impatrq/insonora/Estructura/corte circular de la caja de insonora para que el publico pueda interactuar/Imagen de WhatsApp 2023-11-22 a las 09.19.30_ffd868a9.jpg

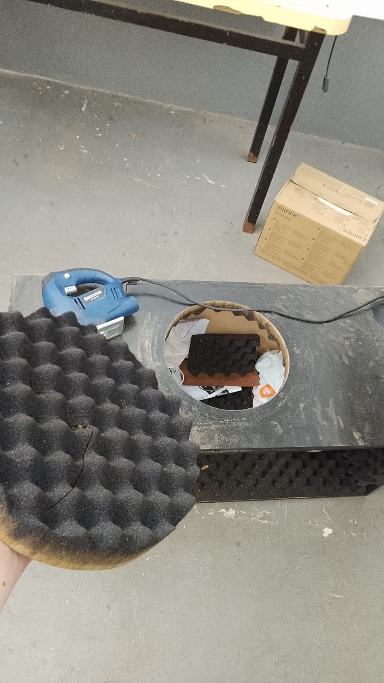
Estructura/corte circular de la caja de insonora para que el publico pueda interactuar/Imagen de WhatsApp 2023-11-22 a las 09.19.30_ffd868a9.jpg
