impatrq/insonora/Estructura/cortes de la madera para hacer la caja de insonora/Imagen de WhatsApp 2023-11-22 a las 09.21.23_7561fe22.jpg

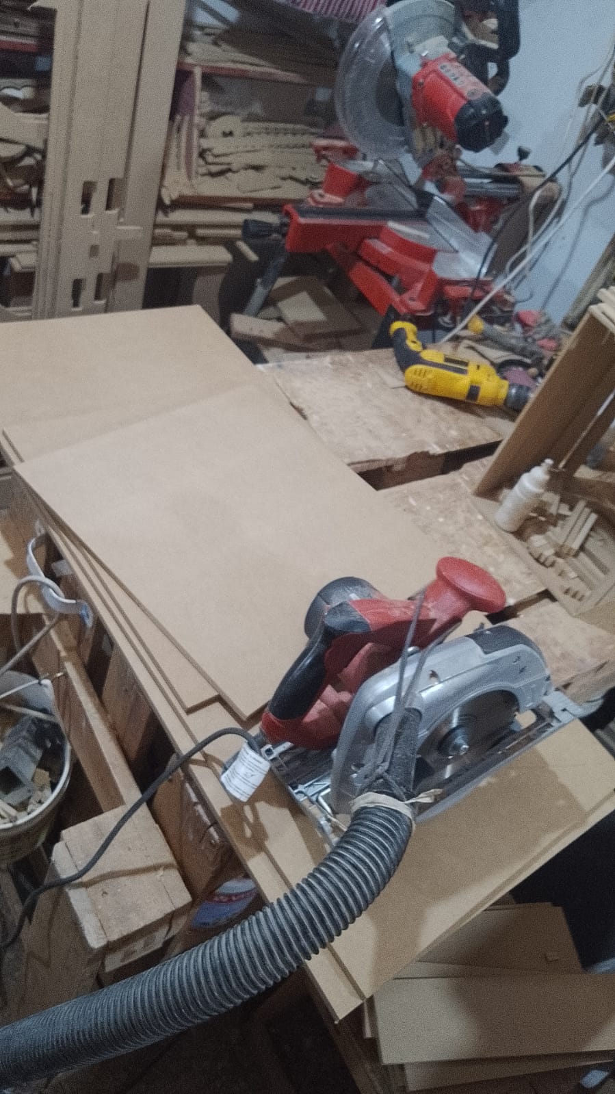
Estructura/cortes de la madera para hacer la caja de insonora/Imagen de WhatsApp 2023-11-22 a las 09.21.23_7561fe22.jpg
