impatrq/insonora/Estructura/disposicion de parlantes/Imagen de WhatsApp 2023-11-22 a las 09.26.25_6fa25fe4.jpg

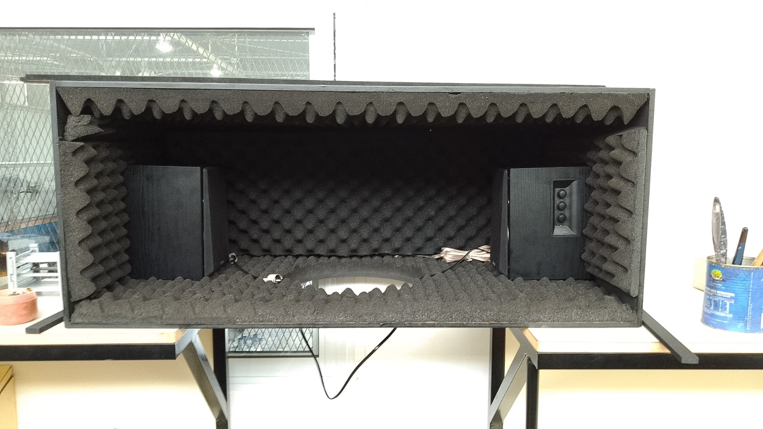
Estructura/disposicion de parlantes/Imagen de WhatsApp 2023-11-22 a las 09.26.25_6fa25fe4.jpg
