impatrq/insonora/Estructura/Imagen de WhatsApp 2023-11-22 a las 09.16.47_289416f6.jpg

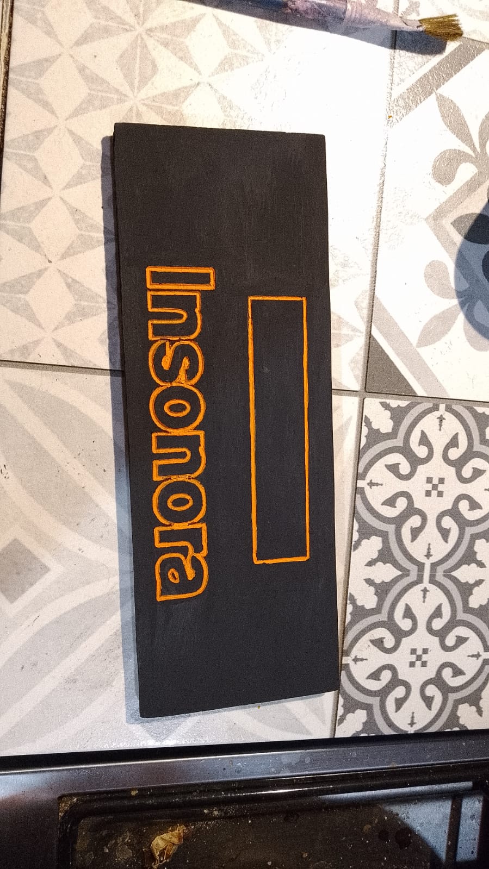
Estructura/Imagen de WhatsApp 2023-11-22 a las 09.16.47_289416f6.jpg
