impatrq/insonora/Estructura/plano a escala de la caja de insonora/Imagen de WhatsApp 2023-11-22 a las 09.17.45_47281ffb.jpg

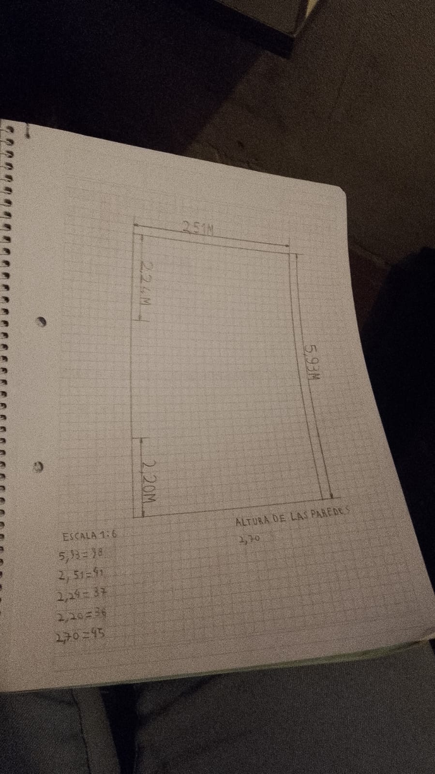
Estructura/plano a escala de la caja de insonora/Imagen de WhatsApp 2023-11-22 a las 09.17.45_47281ffb.jpg
