impatrq/insonora/fotos/pcb-pwm-audio-terminado.jpeg

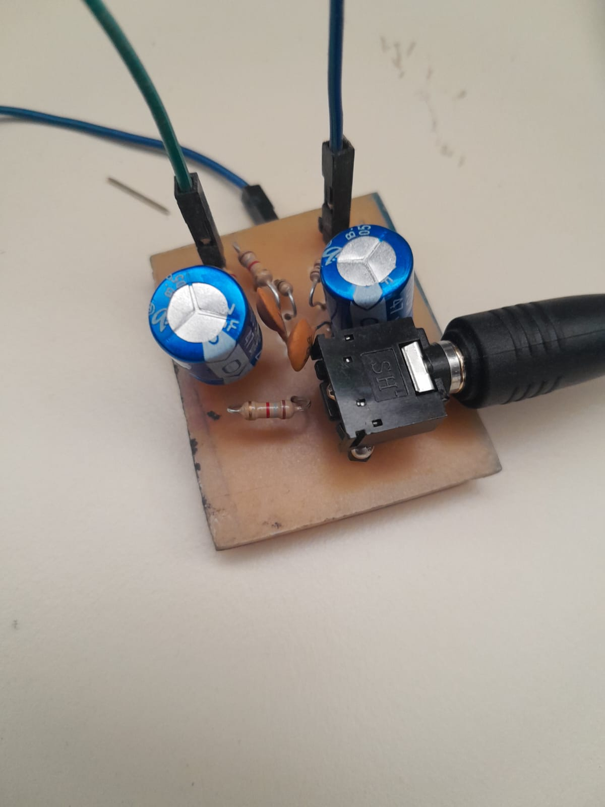
fotos/pcb-pwm-audio-terminado.jpeg
