impatrq/insonora/PCBS/cortes plaquetas de cobre/Imagen de WhatsApp 2023-11-22 a las 09.17.11_49b71000.jpg

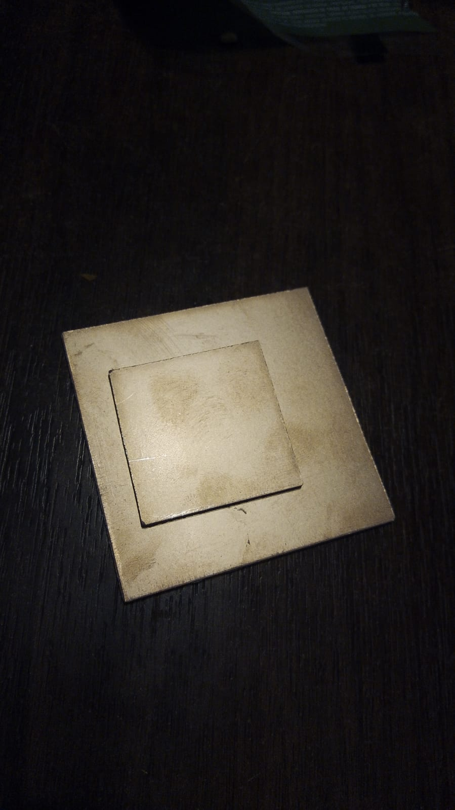
PCBS/cortes plaquetas de cobre/Imagen de WhatsApp 2023-11-22 a las 09.17.11_49b71000.jpg
