impatrq/insonora/Post-no-subidos/Ambientes laborales (1).png

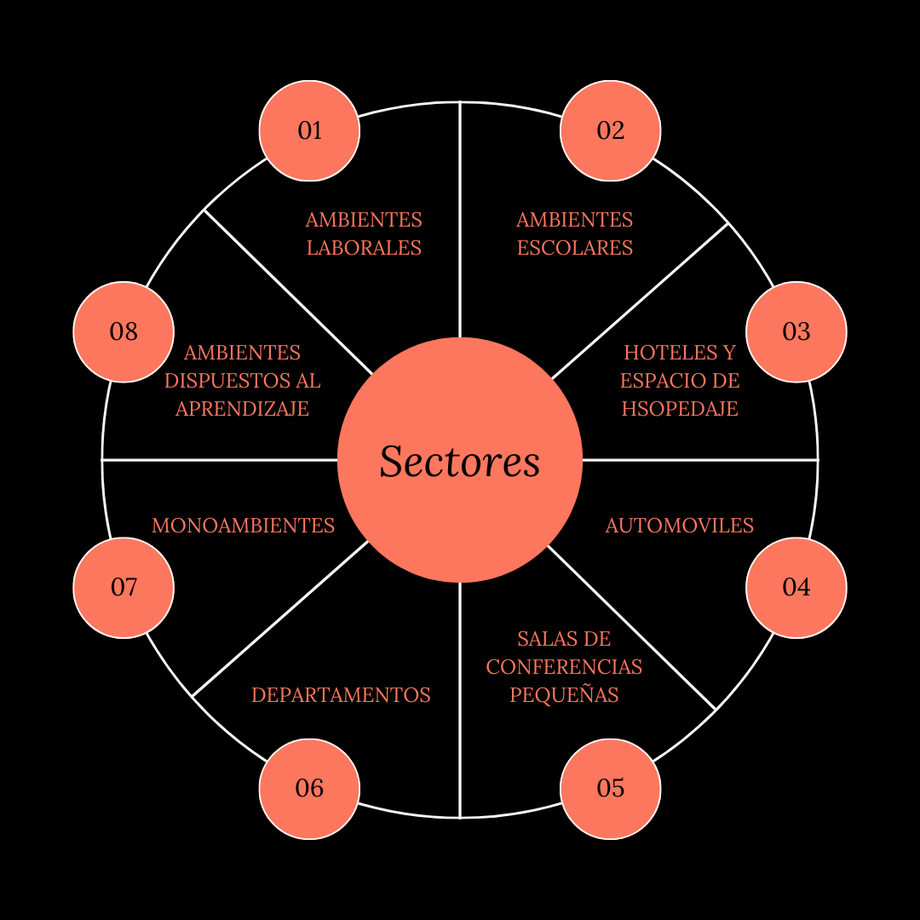
Post-no-subidos/Ambientes laborales (1).png
