impatrq/insonora/Post-no-subidos/beneficios de la descontaminacion sonora (1).png

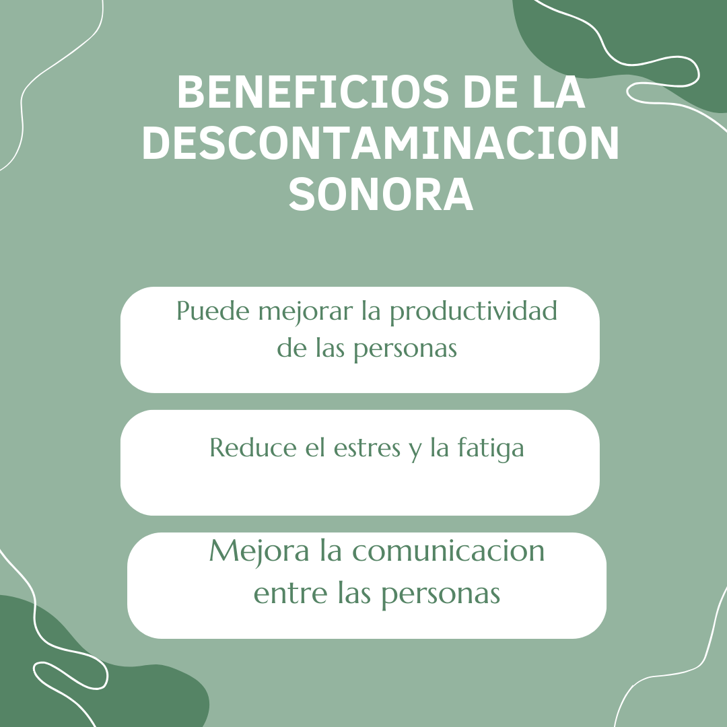
Post-no-subidos/beneficios de la descontaminacion sonora (1).png
