impatrq/insonora/Post-no-subidos/Captura de pantalla 2023-11-24 145829.png

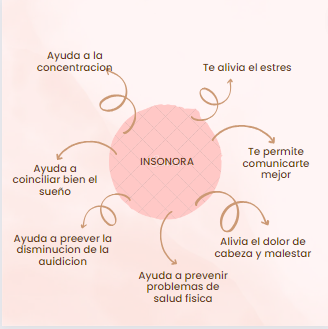
Post-no-subidos/Captura de pantalla 2023-11-24 145829.png
