impatrq/insonora/Post-no-subidos/Desventajas de la contaminacion sonora.png

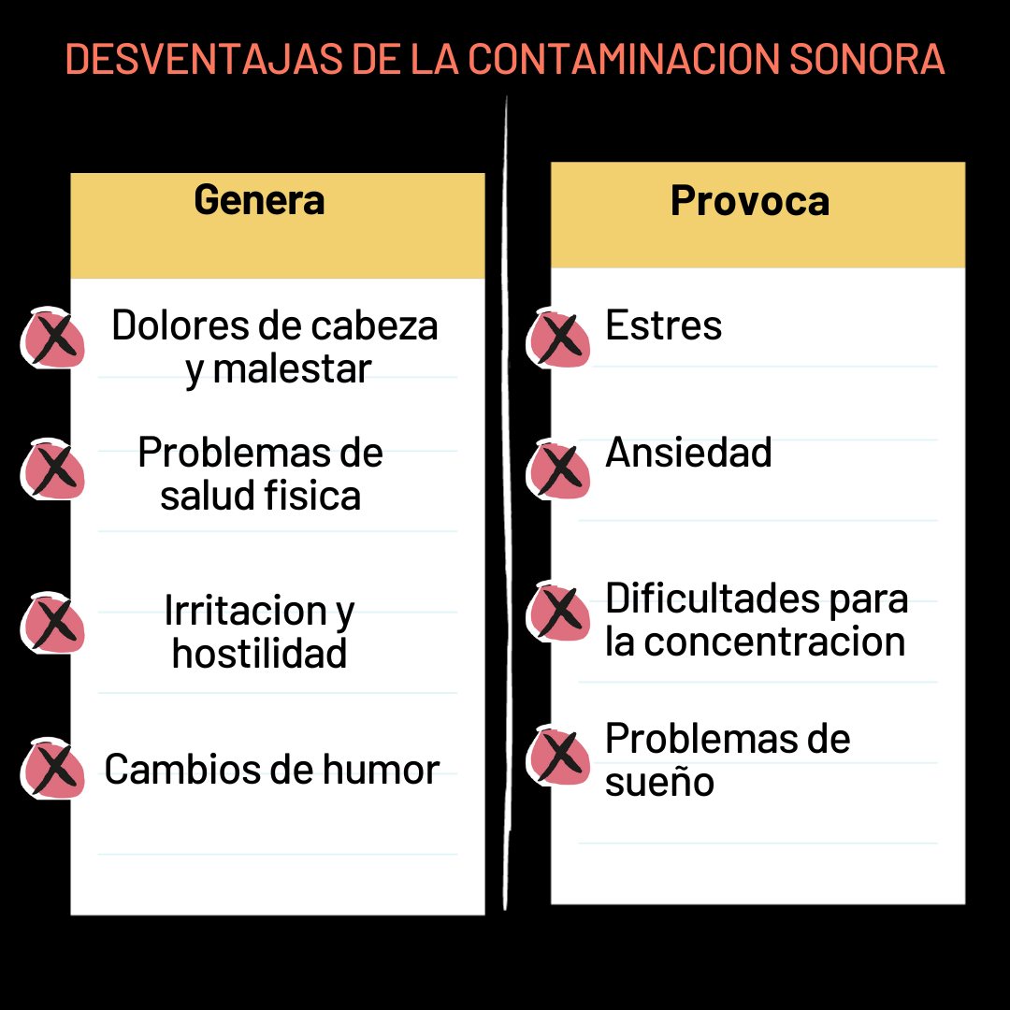
Post-no-subidos/Desventajas de la contaminacion sonora.png
