impatrq/insonora/Post-no-subidos/Dia nacional de la audicion.png

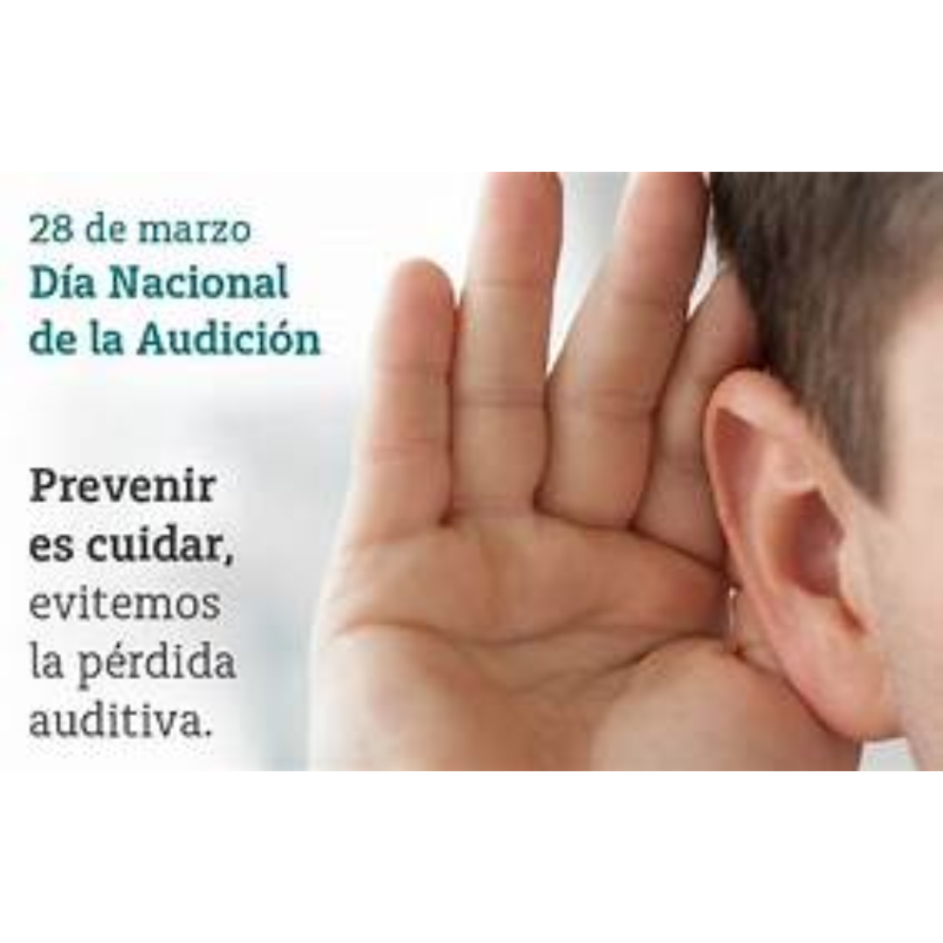
Post-no-subidos/Dia nacional de la audicion.png
