impatrq/insonora/Post-no-subidos/Efectos del ruido.png

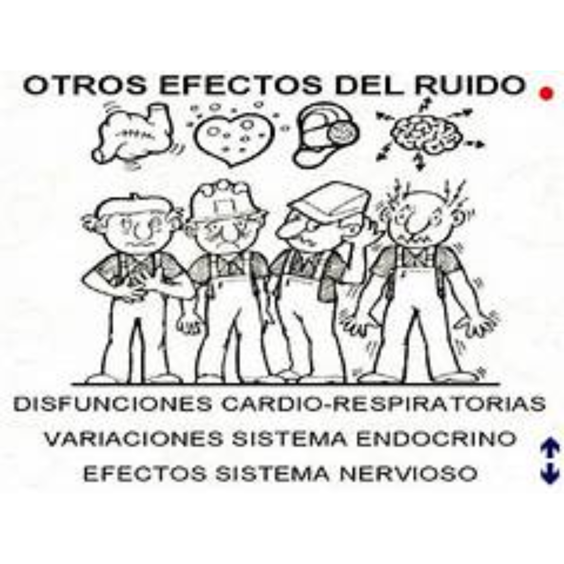
Post-no-subidos/Efectos del ruido.png
