impatrq/insonora/Post-no-subidos/El ruido es un sonido no deseado que puede generar molestias en la sociedad (2).png

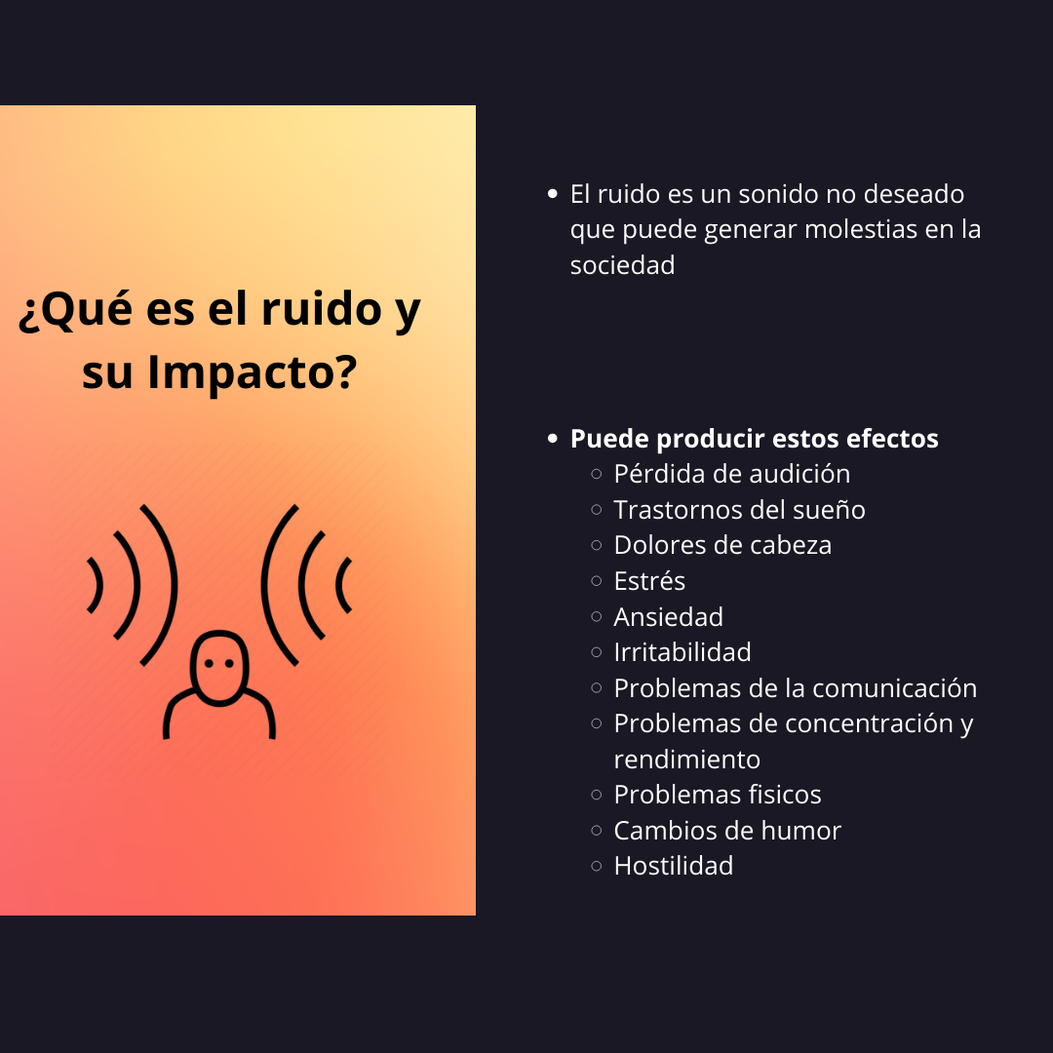
Post-no-subidos/El ruido es un sonido no deseado que puede generar molestias en la sociedad (2).png
