impatrq/insonora/Post-no-subidos/Sabias que.png

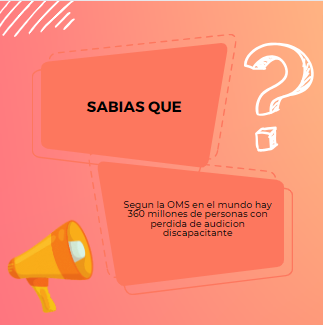
Post-no-subidos/Sabias que.png
