impatrq/insonora/Post-no-subidos/Vengan a vernos el dia viernes 1011 y el dia sabado 1111 a la exposicion anual que se realiza en la escuela tecnica n°7 (1).png

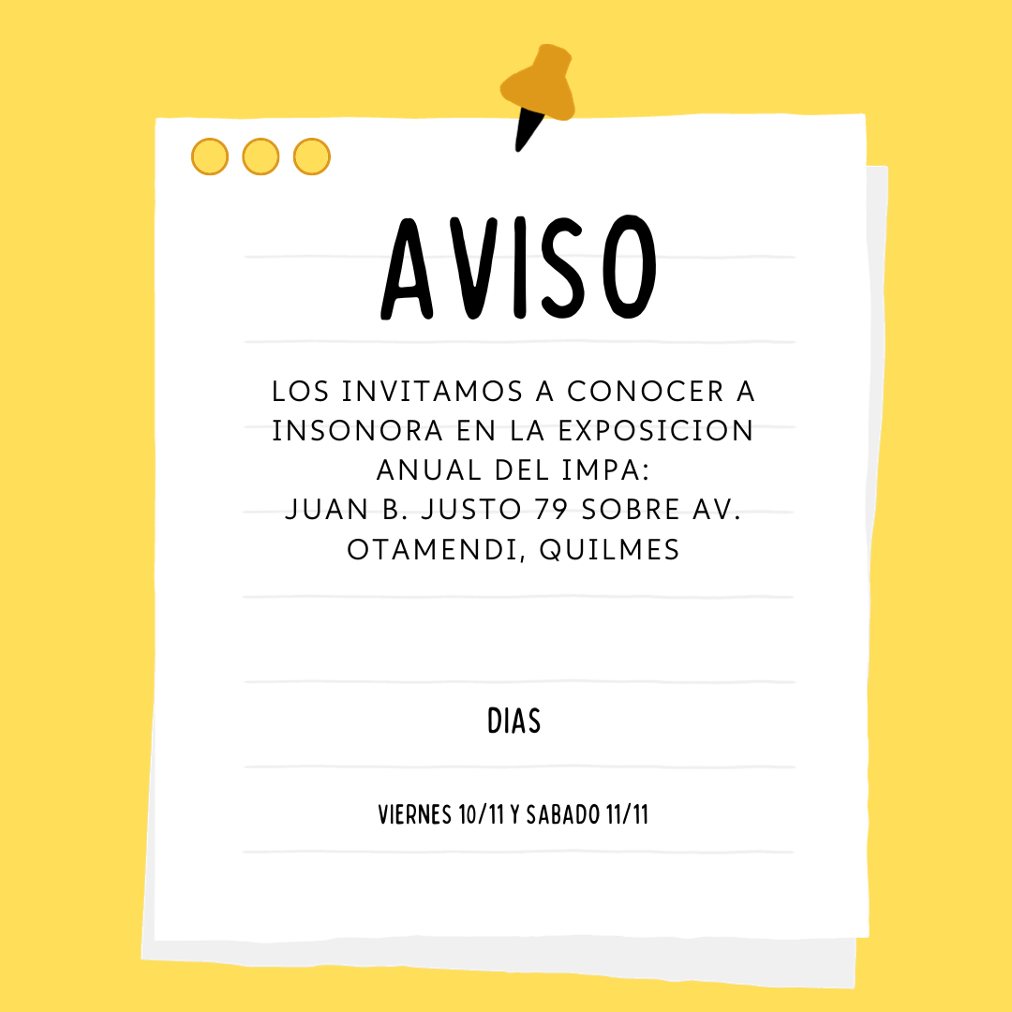
Post-no-subidos/Vengan a vernos el dia viernes 1011 y el dia sabado 1111 a la exposicion anual que se realiza en la escuela tecnica n°7 (1).png
