impatrq/insonora/Post-no-subidos/¿Qué hacer y qué no hacer (1).png

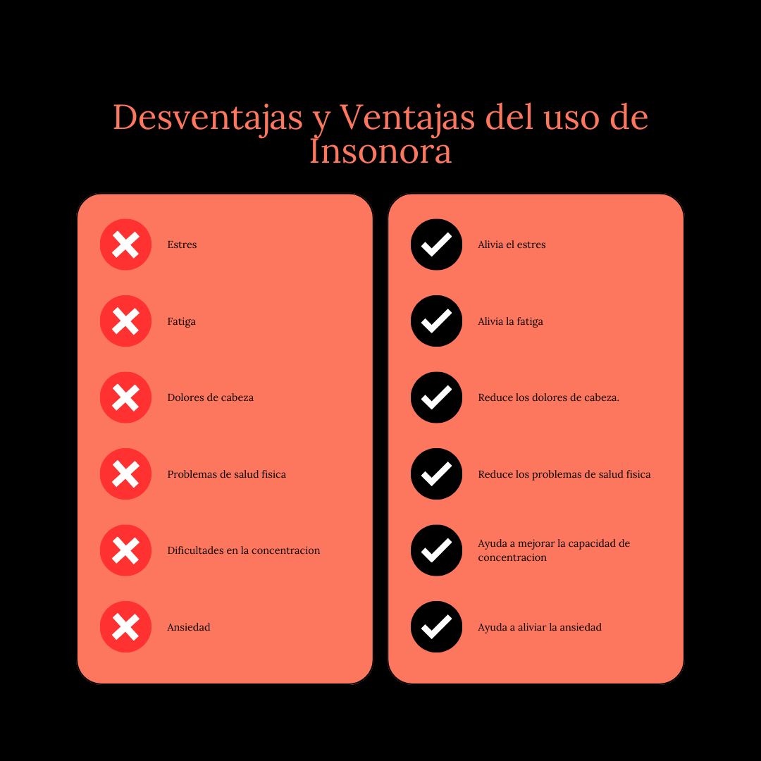
Post-no-subidos/¿Qué hacer y qué no hacer (1).png
