impatrq/insonora/PostSubidos/WhatsApp Image 2023-11-24 at 17.09.22.jpeg

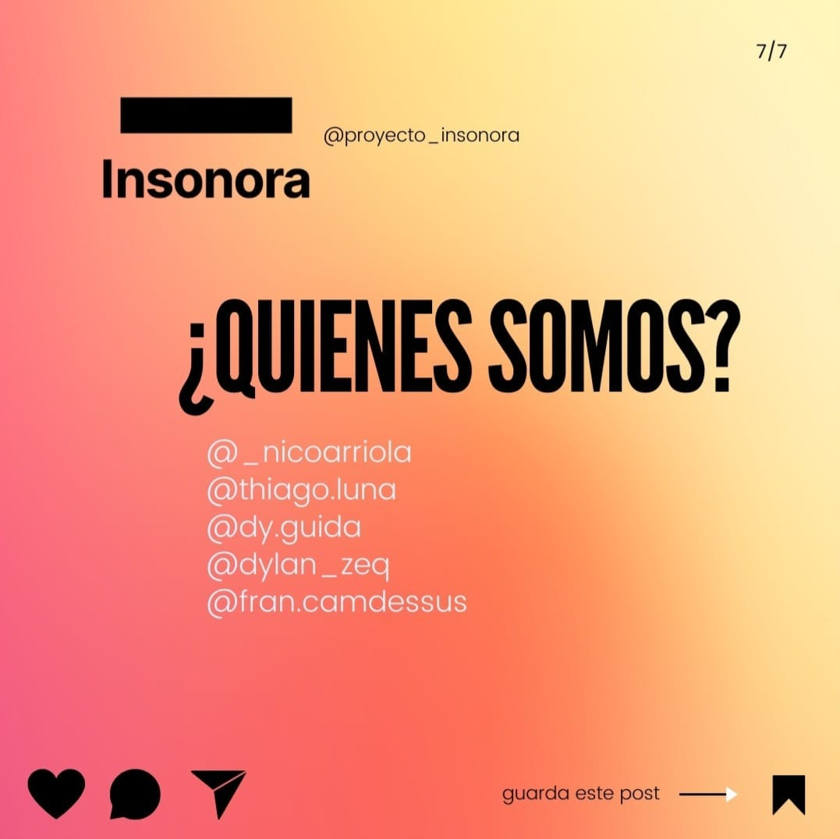
PostSubidos/WhatsApp Image 2023-11-24 at 17.09.22.jpeg
