impatrq/insonora/PostSubidos/WhatsApp Image 2023-11-24 at 17.09.23.jpeg

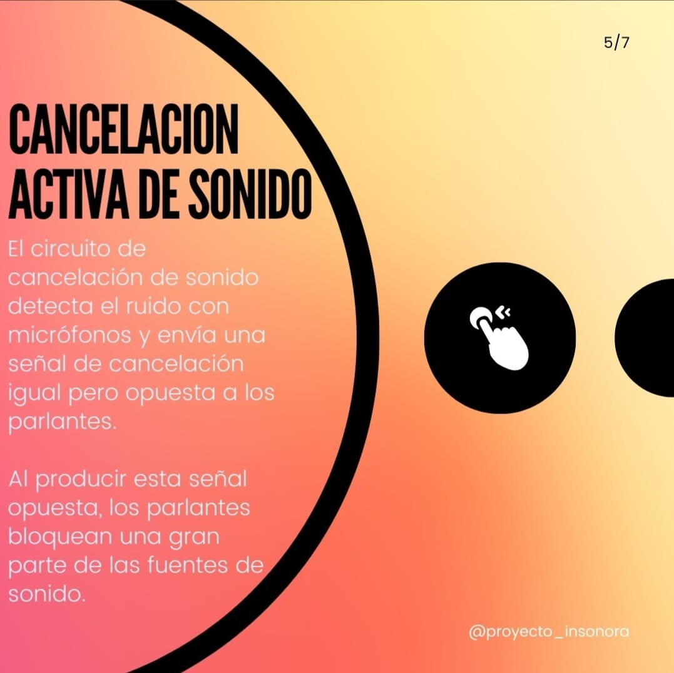
PostSubidos/WhatsApp Image 2023-11-24 at 17.09.23.jpeg
