impatrq/insonora/Presupuesto/Compras/compra de los paneles de insonorizacion/Imagen de WhatsApp 2023-11-22 a las 09.21.08_86655f33.jpg

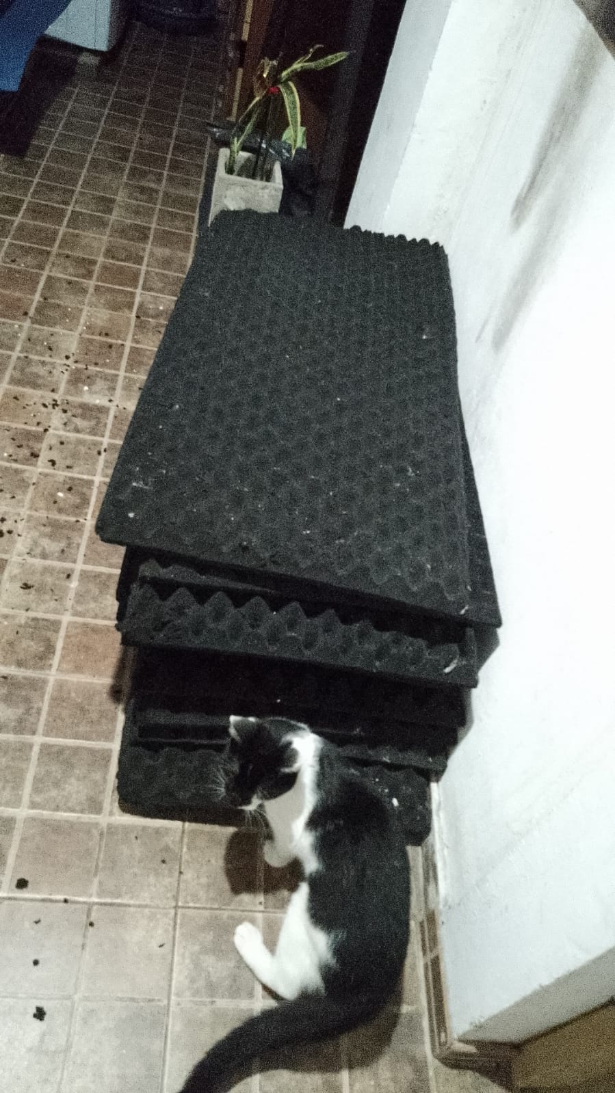
Presupuesto/Compras/compra de los paneles de insonorizacion/Imagen de WhatsApp 2023-11-22 a las 09.21.08_86655f33.jpg
