impatrq/insonora/Programacion/CodigoArduino/FFT_signal.h

#define FFT_N 2048 // Must be a power of 2
#define TOTAL_TIME 0.1853  //The time in which data was captured. This is equal to FFT_N/sampling_freq

float fft_input[FFT_N];
float fft_output[FFT_N];

float max_magnitude = 0;
float fundamental_freq = 0;


/* Dummy data (Output of an accelerometer)
 * Frequency: 5 Hz
 * Amplitude: 0.25g
*/
double fft_signal[FFT_N] = {
11100,10600,11200,11700,12200,12900,12900,13100,11600,12900,13600,13000,12100,11700,11000,11500,10400,10800,9800,9800,9400,9700,8700,8700,8200,8200,7700,7800,7200,7200,6900,5900,5600,7400,8100,8300,8600,9400,9300,9600,10300,11000,10700,11200,11200,11200,11800,11700,12900,12700,12700,11900,11500,11100,11700,13700,12900,11700,10600,11000,10900,11100,9800,9600,9900,9400,9000,8300,8100,7600,7100,7600,7000,9700,8200,8200,7600,7000,7500,8500,8400,9400,9100,9400,10200,10400,10100,10600,11000,11700,11700,12700,12100,12200,12000,12200,14200,13700,12400,11100,11000,11500,10800,10700,10500,10400,9800,9400,9300,9300,9200,9000,8000,7600,7600,7400,7500,3600,6100,6700,9000,8500,7800,8000,8800,9100,10000,9600,10900,10600,11000,11400,11800,11700,11100,12100,12600,13400,11000,12800,12100,13100,12800,12100,11300,10900,11200,10500,10200,9500,9900,9800,9000,8600,8300,8000,7900,7300,6800,6700,9500,9300,7500,7800,7100,8000,8400,8700,8900,10000,10300,10300,9900,10300,11300,11800,12000,11200,12200,13100,13400,13100,13500,12900,13100,10900,11900,11500,11700,10400,10400,10700,9900,10200,9600,9300,8700,8500,8500,8300,8000,7700,6700,7200,4800,6300,8400,8000,7600,8100,9500,9600,9600,9600,10700,10400,11000,10800,11300,11700,11200,11900,12500,12800,12500,10900,12500,12600,11900,11800,11800,11200,11500,11000,10600,10500,9900,9800,9300,8700,9200,8600,7900,7600,7500,6600,7500,7400,8800,6200,6500,7500,8400,8700,8700,9400,9500,10000,10400,10900,11200,11500,11500,11700,11900,13000,12000,13700,12900,11600,13600,12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
};
